HarvardURC/Balancer/CAD_Files/1X CAD/spacer.SLDPRT

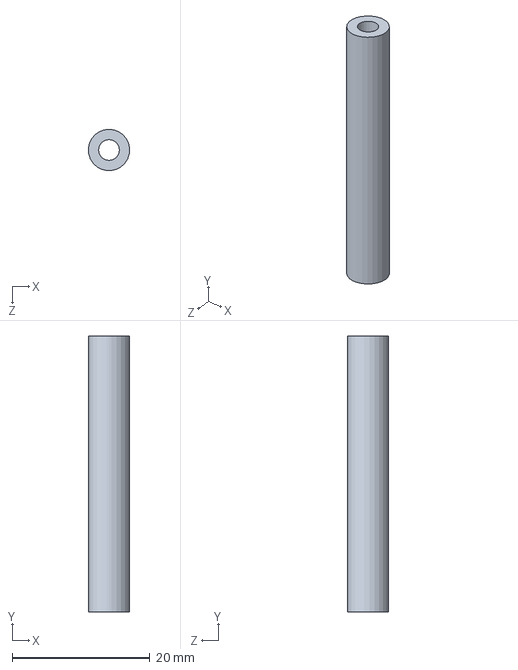
[picture p15: CAD file, 2016-11-20]
CAD_Files/1X CAD/spacer.SLDPRT
5.99 x 40.0 x 6.00 mm
