HarvardURC/Balancer/CAD_Files/1.5x CAD/Empty.DXF

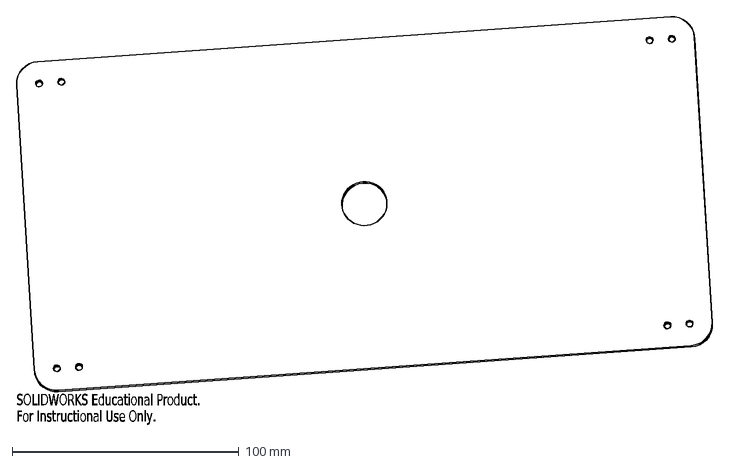
[picture p16: CAD file, 2017-02-11]
CAD_Files/1.5x CAD/Empty.DXF
SOLIDWORKS Educational Product.
For Instructional Use Only.
