HarvardURC/Balancer/CAD_Files/1X CAD/mounting hub.SLDPRT

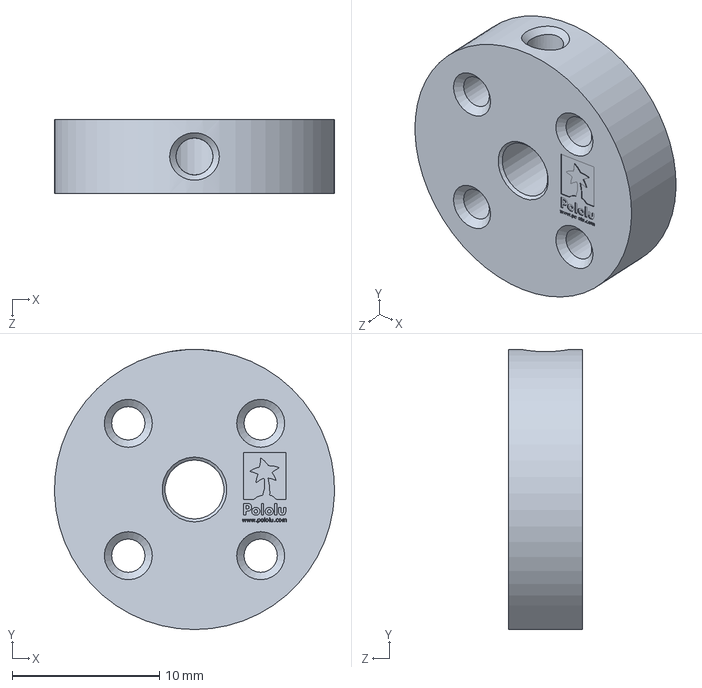
[picture p17: CAD file, 2016-11-12]
CAD_Files/1X CAD/mounting hub.SLDPRT
19.0 x 19.0 x 5.00 mm
