HarvardURC/Balancer/CAD_Files/1.5x CAD/Motor Layer.DXF

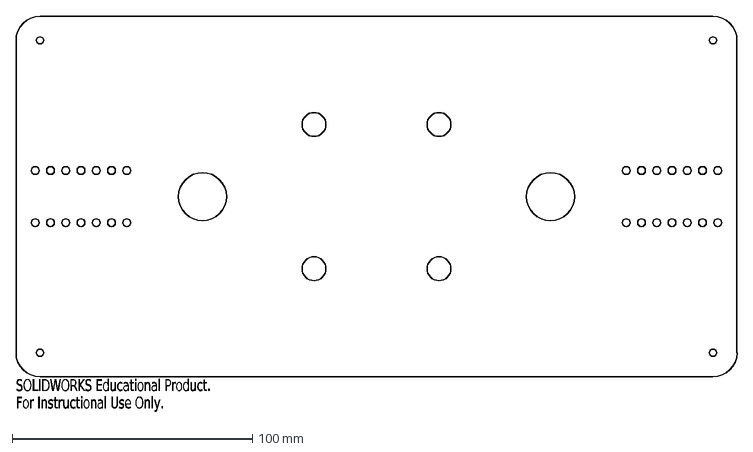
[picture p18: CAD file, 2017-02-11]
CAD_Files/1.5x CAD/Motor Layer.DXF
SOLIDWORKS Educational Product.
For Instructional Use Only.
