HarvardURC/Balancer/CAD_Files/1X CAD/motor mount.SLDPRT

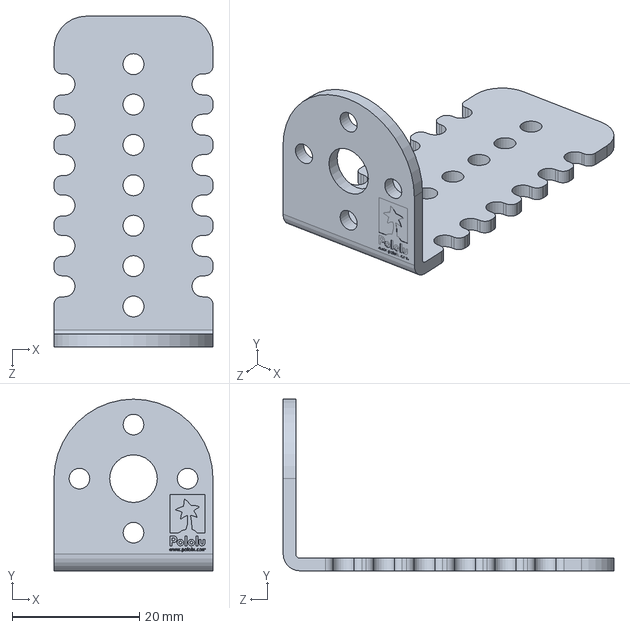
[picture p19: CAD file, 2016-11-12]
CAD_Files/1X CAD/motor mount.SLDPRT
25.0 x 27.0 x 52.0 mm
