HarvardURC/Balancer/CAD_Files/1.5x CAD/mid.SLDPRT

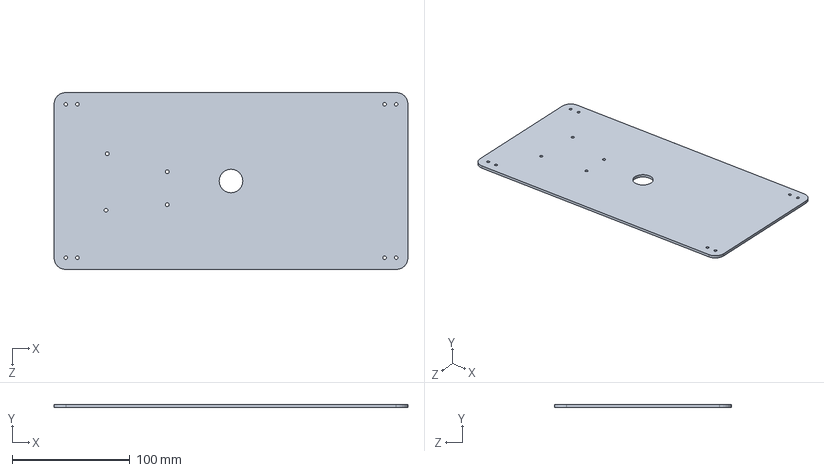
[picture p20: CAD file, 2017-02-08]
CAD_Files/1.5x CAD/mid.SLDPRT
300.0 x 2.60 x 150.0 mm
