HarvardURC/Balancer/CAD_Files/1X CAD/motor.SLDPRT

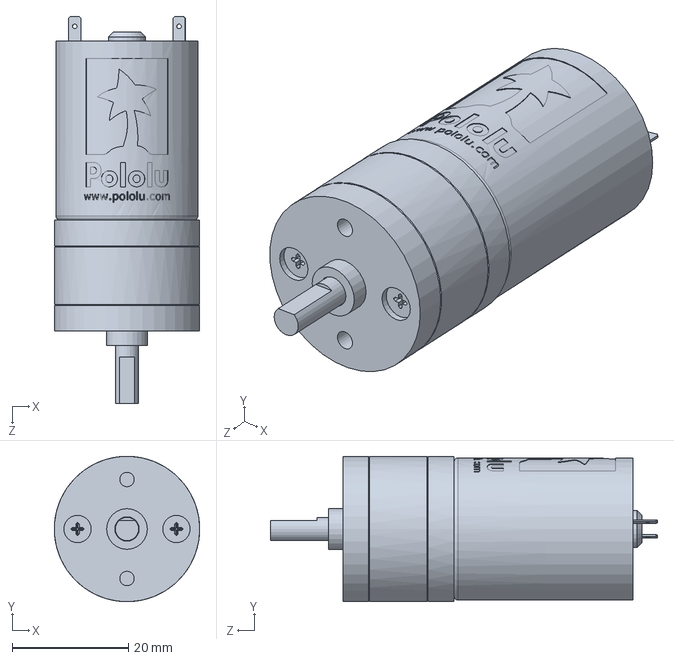
[picture p21: CAD file, 2016-11-12]
CAD_Files/1X CAD/motor.SLDPRT
25.0 x 25.0 x 66.5 mm
