HarvardURC/Balancer/CAD_Files/1.5x CAD/Arduino.SLDPRT

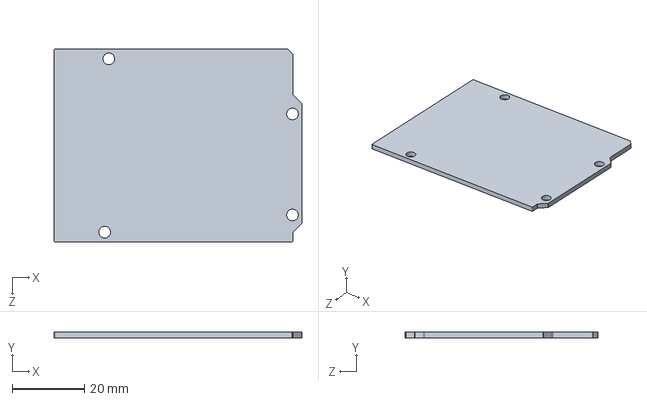
[picture p22: CAD file, 2017-02-08]
CAD_Files/1.5x CAD/Arduino.SLDPRT
68.6 x 1.59 x 53.3 mm
