HarvardURC/Balancer/wireless_sender/wireless_sender.ino

#include <SPI.h>
#include <nRF24L01.h>
#include <RF24.h>

RF24 radio(7, 8);

const byte rxAddr[6] = "00001";

void setup()
{
  radio.begin();
  radio.setRetries(15, 15);
  radio.openWritingPipe(rxAddr);
  
  radio.stopListening();
}

void loop()
{
  const char text[] = "Hi balancer";
  radio.write(&text, sizeof(text));
  
  delay(1000);
}
